aLLUPS/AutoSaw/3dModel/Labeled_3d_model.png

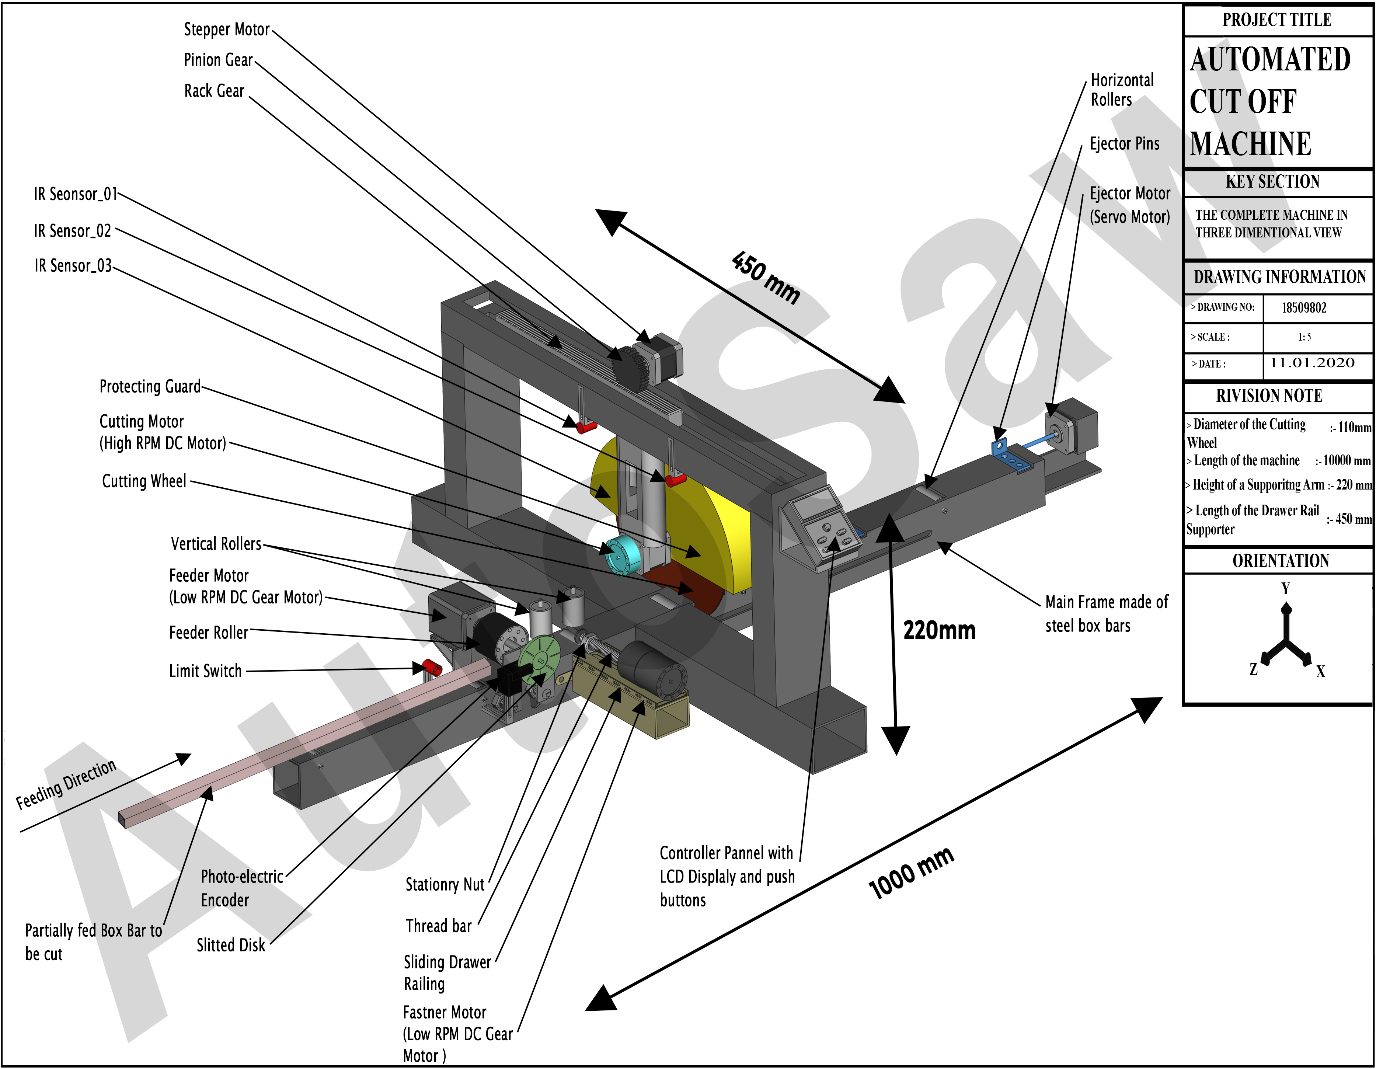
3dModel/Labeled_3d_model.png
