aLLUPS/AutoSaw/PCB/RealWorldImplementation/02 Soldered_back.png

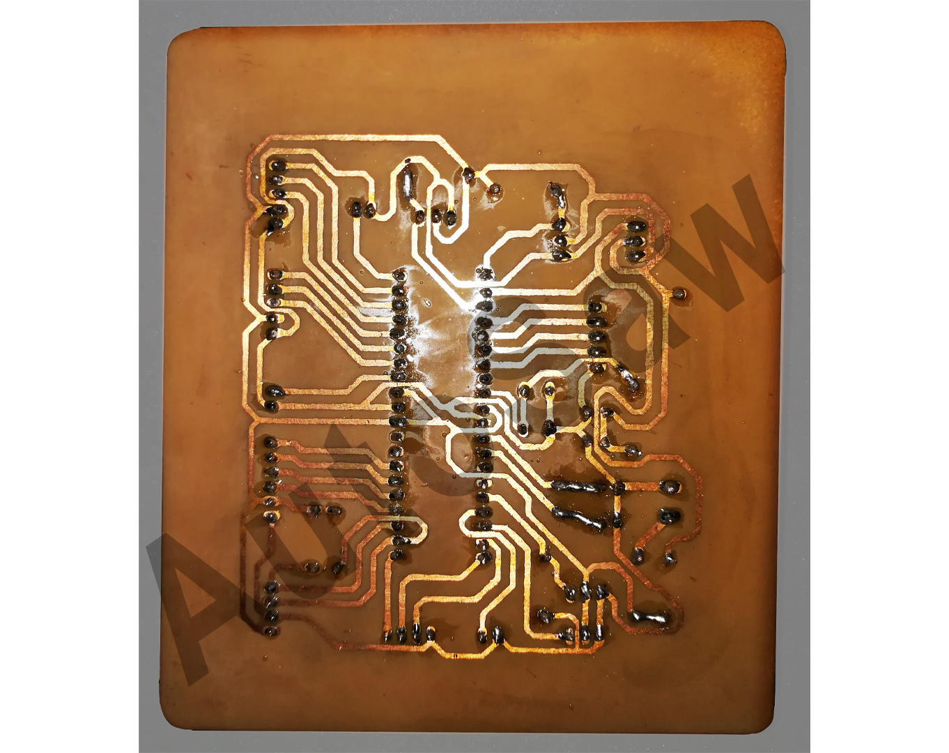
PCB/RealWorldImplementation/02 Soldered_back.png
